Gueni/Raspberry-compute-module-4-gateway/6.png

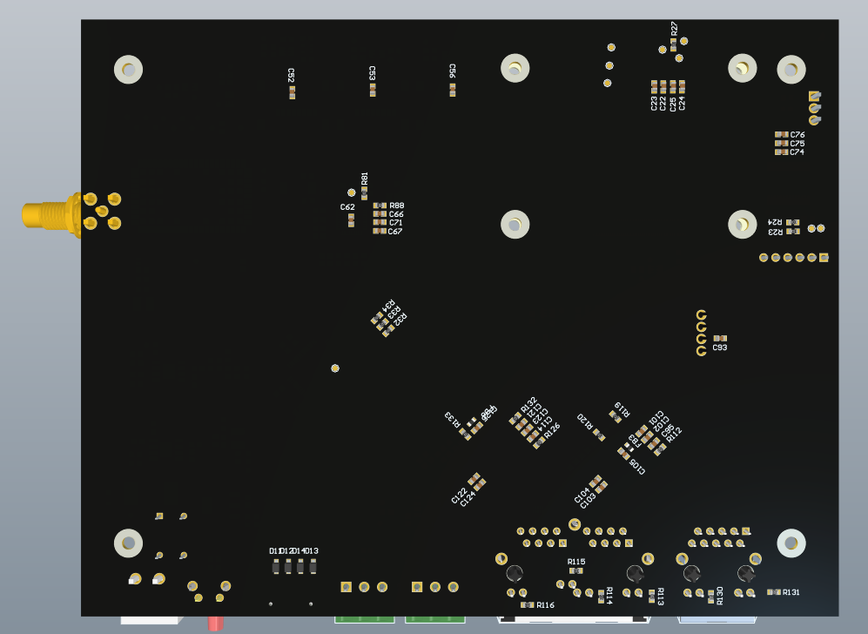
6.png
