Gueni/Raspberry-compute-module-4-gateway/7.png

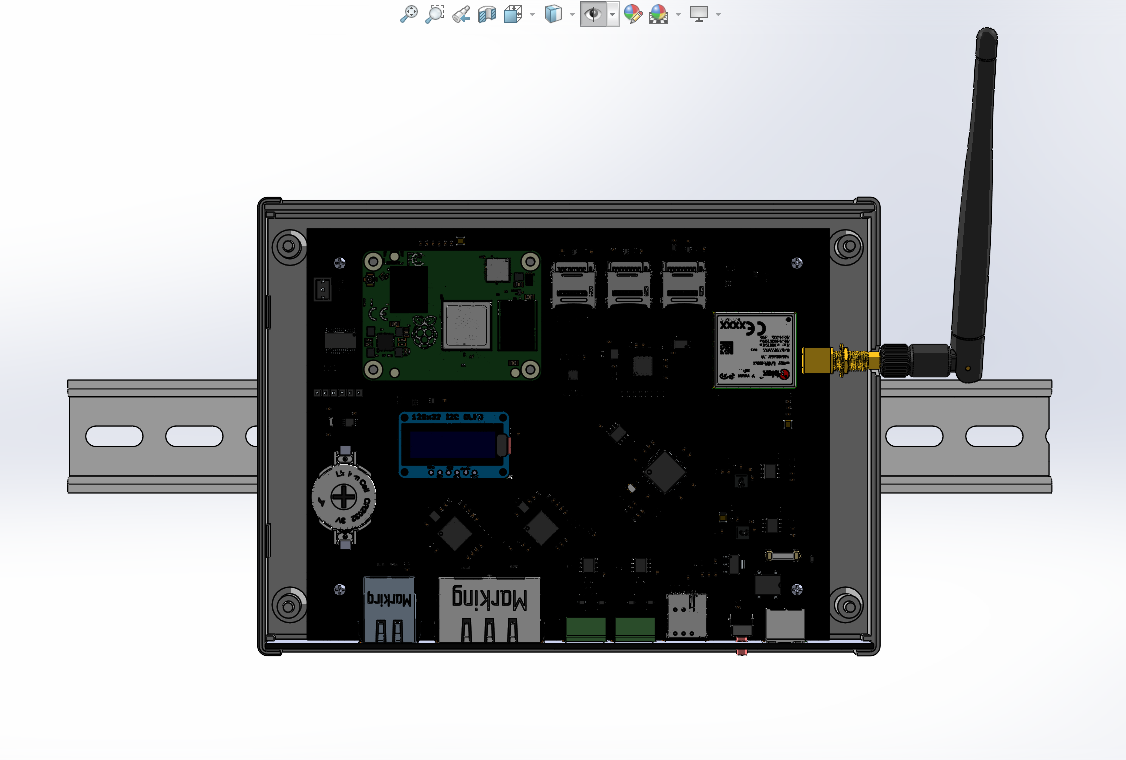
7.png
