Gueni/Raspberry-compute-module-4-gateway/LCD pyscripts/oled.py

import time
import busio
from board import SCL, SDA
from oled_text import OledText, Layout64, BigLine, SmallLine

i2c = busio.I2C(SCL, SDA)
oled = OledText(i2c, 128, 64)
oled.layout = Layout64.layout_icon_only()
oled.text('\uf58b', 1)
time.sleep(2)
oled.layout = Layout64.layout_5small()
for i in range(1, 6):
	oled.text("Hello Line {}".format(i), i)
time.sleep(1)
oled.layout = Layout64.layout_1big_3small()
oled.auto_show = False
oled.text("The Title", 1)
oled.text("Line 2 text", 2)
oled.text("Line 3 text", 3)
oled.text("Line 4 text", 4)
oled.show()
oled.auto_show = True
time.sleep(2)
oled.layout = Layout64.layout_3medium_3icons()
oled.auto_show = False
oled.text("Temperature: ", 1)
oled.text("Light: ", 2)
oled.text("Humidity: ", 3)
oled.text('\uf062', 4)
oled.text('\uf061', 5)
oled.text('\uf063', 6)
oled.show()
oled.auto_show = True
time.sleep(0.5)
oled.text('\uf063', 4)
time.sleep(2)
oled.layout = Layout64.layout_icon_1big_2small()
oled.auto_show = False
oled.text('\uf58b', 1)
oled.text("Meow!", 2)
oled.text("I am the", 3)
oled.text("cool cat", 4)
oled.show()
oled.auto_show = True
time.sleep(3)
oled.layout = {
	1: SmallLine(0, 0),
	2: BigLine(5, 15, font="Arimo.ttf", size=24),
	3: BigLine(5, 40, font="Arimo.ttf", size=18)
}
oled.text("I want my layout!")
oled.text("Custom 1", 2)
oled.text("Custom 2", 3)
time.sleep(3)
oled.layout = Layout64.layout_1big_center()
oled.on_draw = lambda draw: draw.rectangle((0, 0, 127, 63), outline=255, fill=0)
oled.text("The Fat Cat", 1)
time.sleep(4)
oled.clear()
